madhukartemba/ir_hub/3D Print/Version 0/Led Ring.stl

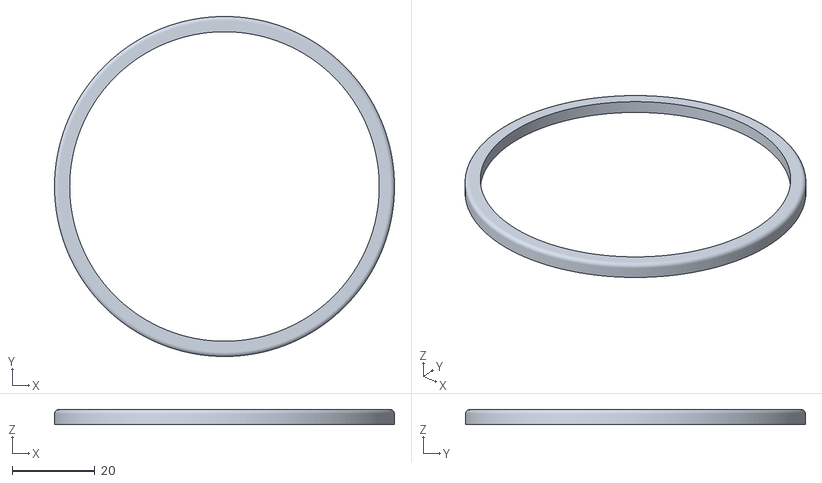
[picture p15: CAD file, 2025-08-03, an earlier design]
3D Print/Version 0/Led Ring.stl
82.4 x 82.4 x 3.60
