madhukartemba/ir_hub/3D Print/Version 1/Base5of5.stl

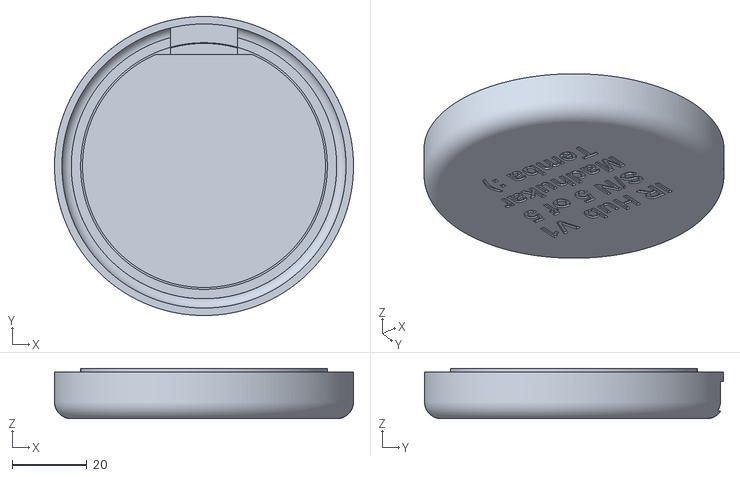
[picture p16: CAD file, 2025-08-30, an earlier design]
3D Print/Version 1/Base5of5.stl
80.0 x 80.0 x 13.5
