madhukartemba/ir_hub/3D Print/Version 0/Speaker Holder.stl

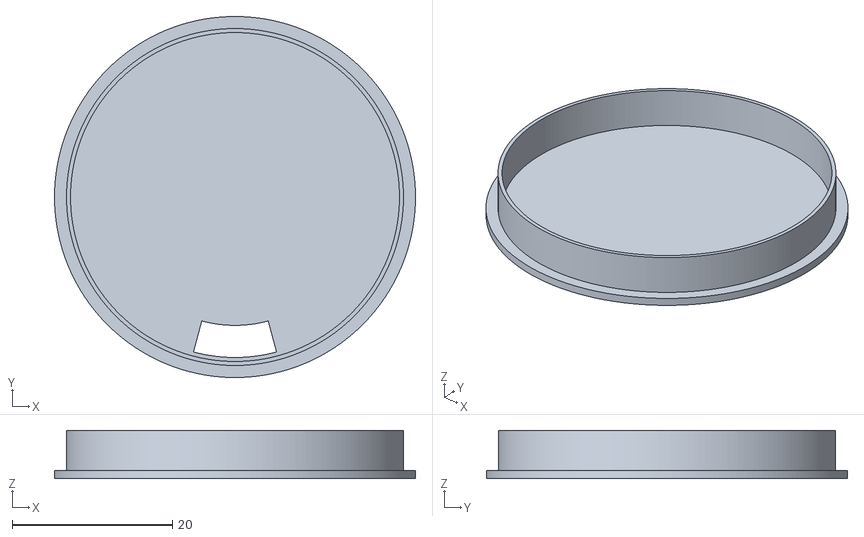
[picture p17: CAD file, 2025-08-03, an earlier design]
3D Print/Version 0/Speaker Holder.stl
45.0 x 45.0 x 6.00
