madhukartemba/ir_hub/src/UI/settings/Settings.h

#include <ESP.h>
#include "../../global/Global.h"
#include "../../preferences.h"
#include "../../utils/MenuUtils.h"
#include "ClearDataConfirmation.h"
#include "DisableAlexaConfirmation.h"
#include "FactoryResetConfirmation.h"
#include "MqttStatusDetailScreen.h"
#include "ResetWiFiConfirmation.h"
#include "SystemInfoScreen.h"
#include "UpdateCheckScreen.h"
#include "UserPrefs.h"

class Settings : public Screen {
   private:
    enum class MenuLevel {
        ROOT,
        PREFERENCES,
        CONNECTIVITY,
        UPDATES,
        SYSTEM,
        DATA_RESET,
    };

    enum class Action {
        OPEN_PREFERENCES,
        OPEN_CONNECTIVITY,
        OPEN_UPDATES,
        OPEN_SYSTEM,
        OPEN_DATA_RESET,
        SOUND,
        ALEXA,
        HAPTICS,
        FIRMWARE_INFO,
        LAST_CHECK_INFO,
        UPDATE_STATUS_INFO,
        MQTT_STATUS_INFO,
        INFO_SCREEN,
        CHECK_UPDATE,
        RESTART,
        CLEAR_DATA,
        WIFI_WIPE,
        FACTORY_RESET,
        BACK,
    };

    static constexpr int kMaxItems = 14;
    const char* menuItems[kMaxItems];
    Action menuActions[kMaxItems];
    int menuCount = 0;
    MenuLevel currentMenu = MenuLevel::ROOT;

    int selectedIndex = 0;
    bool isRestarting = false;
    unsigned long restartStartTime = 0;
    bool hasHaptics = false;
    bool hasOta = false;

    char firmwareLabel[28] = "Firmware: --";
    char lastCheckLabel[28] = "Last check: --";
    char updateStatusLabel[28] = "Status: Never checked";
    char mqttStatusLabel[24] = "MQTT: --";

   public:
    void onEnter() override {
        LOG_DEBUG("[Settings] onEnter");

        hasHaptics = haptics.isPresent();  // isPresent, not isReady (uncalibrated chip)
        hasOta = otaUpdater.isEnabled();
        currentMenu = MenuLevel::ROOT;
        buildMenuForCurrentLevel();
        selectedIndex = 0;
        isRestarting = false;

        ledRing.breathe(COLOR_SETTINGS);

        button.setClickCallback([this]() {
            LOG_DEBUG("[Settings] onButtonClick");
            if (isRestarting) {
                return;
            }
            selectedIndex = (selectedIndex + 1) % menuCount;
        });

        button.setLongPressCallback([this]() {
            LOG_DEBUG("[Settings] onButtonLongPress");
            if (isRestarting) {
                return;
            }
            handleAction(menuActions[selectedIndex]);
        });
    }

    void onUpdate() override {
        display.clear();

        if (isRestarting) {
            drawRestarting();
            if (millis() - restartStartTime > 2000) {
                ESP.restart();
            }
        } else {
            refreshDynamicLabels();
            drawMenu();
        }

        display.update();
    }

    void onExit() override { LOG_DEBUG("[Settings] onExit"); }

   private:
    void buildMenuForCurrentLevel() {
        menuCount = 0;

        switch (currentMenu) {
            case MenuLevel::ROOT:
                addRow(Action::OPEN_PREFERENCES);
                addRow(Action::OPEN_CONNECTIVITY);
                addRow(Action::OPEN_UPDATES);
                addRow(Action::OPEN_SYSTEM);
                addRow(Action::OPEN_DATA_RESET);
                addRow(Action::BACK);
                break;
            case MenuLevel::PREFERENCES:
                addRow(Action::SOUND);
                if (hasHaptics) {
                    addRow(Action::HAPTICS);
                }
                addRow(Action::BACK);
                break;
            case MenuLevel::CONNECTIVITY:
                addRow(Action::WIFI_WIPE);
                addRow(Action::ALEXA);
                addRow(Action::MQTT_STATUS_INFO);
                addRow(Action::BACK);
                break;
            case MenuLevel::UPDATES:
                if (hasOta) {
                    addRow(Action::CHECK_UPDATE);
                    addRow(Action::FIRMWARE_INFO);
                    addRow(Action::LAST_CHECK_INFO);
                    addRow(Action::UPDATE_STATUS_INFO);
                } else {
                    addRow(Action::UPDATE_STATUS_INFO);
                }
                addRow(Action::BACK);
                break;
            case MenuLevel::SYSTEM:
                addRow(Action::INFO_SCREEN);
                addRow(Action::RESTART);
                addRow(Action::BACK);
                break;
            case MenuLevel::DATA_RESET:
                addRow(Action::CLEAR_DATA);
                addRow(Action::FACTORY_RESET);
                addRow(Action::BACK);
                break;
        }
    }

    void addRow(Action action) {
        if (menuCount >= kMaxItems) {
            return;
        }
        menuActions[menuCount] = action;
        menuItems[menuCount] = labelFor(action);
        menuCount++;
    }

    void refreshDynamicLabels() {
        if (hasOta) {
            refreshOtaInfoLabels();
        }
        refreshMqttStatusLabel();
        for (int i = 0; i < menuCount; i++) {
            menuItems[i] = labelFor(menuActions[i]);
        }
    }

    void refreshOtaInfoLabels() {
        snprintf(firmwareLabel, sizeof(firmwareLabel), "Firmware: v%s",
                 otaUpdater.currentVersion());

        if (!otaUpdater.hasCompletedCheck()) {
            snprintf(lastCheckLabel, sizeof(lastCheckLabel), "Last check: --");
        } else {
            unsigned long ageMin = otaUpdater.lastCheckAgeMs() / 60000UL;
            if (ageMin < 60UL) {
                snprintf(lastCheckLabel, sizeof(lastCheckLabel), "Last check: %lum ago", ageMin);
            } else {
                unsigned long ageHours = ageMin / 60UL;
                snprintf(lastCheckLabel, sizeof(lastCheckLabel), "Last check: %luh ago", ageHours);
            }
        }

        snprintf(updateStatusLabel, sizeof(updateStatusLabel), "Status: %s",
                 otaUpdater.lastCheckStatusText());
    }

    void refreshMqttStatusLabel() {
        if (!wifiManager.isConnected()) {
            snprintf(mqttStatusLabel, sizeof(mqttStatusLabel), "MQTT: Offline");
            return;
        }
        if (!mqttConnector.isEnabled()) {
            snprintf(mqttStatusLabel, sizeof(mqttStatusLabel), "MQTT: Disabled");
            return;
        }
        if (mqttConnector.isConnected()) {
            snprintf(mqttStatusLabel, sizeof(mqttStatusLabel), "MQTT: Connected");
            return;
        }
        if (mqttConnector.hasError()) {
            snprintf(mqttStatusLabel, sizeof(mqttStatusLabel), "MQTT: Error");
            return;
        }
        snprintf(mqttStatusLabel, sizeof(mqttStatusLabel), "MQTT: Connecting");
    }

    const char* labelFor(Action action) {
        switch (action) {
            case Action::OPEN_PREFERENCES:
                return "Preferences";
            case Action::OPEN_CONNECTIVITY:
                return "Connectivity";
            case Action::OPEN_UPDATES:
                return "Updates";
            case Action::OPEN_SYSTEM:
                return "System";
            case Action::OPEN_DATA_RESET:
                return "Reset";
            case Action::SOUND:
                return userPrefsSoundEnabled() ? "Sound: On" : "Sound: Off";
            case Action::ALEXA:
                return userPrefsAlexaEnabled() ? "Alexa: On" : "Alexa: Off";
            case Action::HAPTICS:
                return userPrefsHapticsEnabled() ? "Haptics: On" : "Haptics: Off";
            case Action::FIRMWARE_INFO:
                return firmwareLabel;
            case Action::LAST_CHECK_INFO:
                return lastCheckLabel;
            case Action::UPDATE_STATUS_INFO:
                return updateStatusLabel;
            case Action::MQTT_STATUS_INFO:
                return mqttStatusLabel;
            case Action::INFO_SCREEN:
                return "Info";
            case Action::CHECK_UPDATE:
                return "Check for Updates";
            case Action::RESTART:
                return "Restart";
            case Action::CLEAR_DATA:
                return "Remove Devices";
            case Action::WIFI_WIPE:
                return "Configure Wi-Fi/MQTT";
            case Action::FACTORY_RESET:
                return "Factory Reset";
            case Action::BACK:
                return "Back";
        }
        return "?";
    }

    void handleAction(Action action) {
        switch (action) {
            case Action::OPEN_PREFERENCES:
                currentMenu = MenuLevel::PREFERENCES;
                selectedIndex = 0;
                buildMenuForCurrentLevel();
                break;
            case Action::OPEN_CONNECTIVITY:
                currentMenu = MenuLevel::CONNECTIVITY;
                selectedIndex = 0;
                buildMenuForCurrentLevel();
                break;
            case Action::OPEN_UPDATES:
                currentMenu = MenuLevel::UPDATES;
                selectedIndex = 0;
                buildMenuForCurrentLevel();
                break;
            case Action::OPEN_SYSTEM:
                currentMenu = MenuLevel::SYSTEM;
                selectedIndex = 0;
                buildMenuForCurrentLevel();
                break;
            case Action::OPEN_DATA_RESET:
                currentMenu = MenuLevel::DATA_RESET;
                selectedIndex = 0;
                buildMenuForCurrentLevel();
                break;
            case Action::SOUND:
                toggleSound();
                break;
            case Action::ALEXA:
                toggleAlexa();
                break;
            case Action::HAPTICS:
                toggleHaptics();
                break;
            case Action::FIRMWARE_INFO:
            case Action::LAST_CHECK_INFO:
            case Action::UPDATE_STATUS_INFO:
                // Read-only rows.
                speaker.shortBeep();
                break;
            case Action::MQTT_STATUS_INFO:
                speaker.shortBeep();
                router.push(new MqttStatusDetailScreen());
                break;
            case Action::INFO_SCREEN:
                LOG_DEBUG("[Settings] onButtonLongPress INFO_SCREEN");
                speaker.shortBeep();
                router.push(new SystemInfoScreen());
                break;
            case Action::CHECK_UPDATE:
                LOG_DEBUG("[Settings] onButtonLongPress CHECK_UPDATE");
                speaker.shortBeep();
                router.push(new UpdateCheckScreen());
                break;
            case Action::RESTART:
                LOG_DEBUG("[Settings] onButtonLongPress RESTART");
                isRestarting = true;
                restartStartTime = millis();
                break;
            case Action::CLEAR_DATA:
                LOG_DEBUG("[Settings] onButtonLongPress CLEAR_DATA");
                router.push(new ClearDataConfirmation());
                break;
            case Action::WIFI_WIPE:
                LOG_DEBUG("[Settings] onButtonLongPress WIFI_WIPE");
                router.push(new ResetWiFiConfirmation());
                break;
            case Action::FACTORY_RESET:
                LOG_DEBUG("[Settings] onButtonLongPress FACTORY_RESET");
                router.push(new FactoryResetConfirmation());
                break;
            case Action::BACK:
                if (currentMenu == MenuLevel::ROOT) {
                    LOG_DEBUG("[Settings] onButtonLongPress BACK (root)");
                    router.pop();
                } else {
                    LOG_DEBUG("[Settings] onButtonLongPress BACK (submenu)");
                    currentMenu = MenuLevel::ROOT;
                    selectedIndex = 0;
                    buildMenuForCurrentLevel();
                }
                break;
        }
    }

    void toggleSound() {
        bool newState = !userPrefsSoundEnabled();
        userPrefsSetSoundEnabled(newState);
        speaker.setMuted(!newState);
        if (newState) {
            speaker.shortBeep();  // confirmation only when turning ON
        }
        LOG_INFO("[Settings] Sound %s", newState ? "ON" : "OFF");
    }

    void toggleHaptics() {
        bool newState = !userPrefsHapticsEnabled();
        userPrefsSetHapticsEnabled(newState);

        if (newState) {
            // Lazy auto-calibration on first re-enable this boot. The LRA
            // buzzes briefly during cal — that's expected user feedback.
            if (!haptics.isReady() && haptics.isPresent()) {
                display.clear();
                display.setTextSize(1);
                display.printCentered("Calibrating", 24);
                display.printCentered("haptics...", 36);
                display.update();
                if (!haptics.begin()) {
                    LOG_WARN("[Settings] DRV2605 calibration failed");
                }
            }
            haptics.setMuted(false);
            if (haptics.isReady()) {
                haptics.playSelection();
            }
        } else {
            haptics.setMuted(true);
        }

        LOG_INFO("[Settings] Haptics %s", newState ? "ON" : "OFF");
    }

    void toggleAlexa() {
        bool currentlyEnabled = userPrefsAlexaEnabled();
        if (currentlyEnabled) {
            // Disabling needs explicit confirmation.
            router.push(new DisableAlexaConfirmation());
            return;
        }

        userPrefsSetAlexaEnabled(true);
        speaker.shortBeep();

        if (wifiManager.isConnected()) {
            alexaConnector.begin();
        }
        LOG_INFO("[Settings] Alexa ON");
    }

    void drawMenu() {
        display.setTextSize(1);
        display.printCentered(titleForCurrentMenu(), 0);
        display.drawLine(0, 12, display.getWidth(), 12);
        MenuUtils::drawScrollableMenu(menuItems, menuCount, selectedIndex, 3, 20);
    }

    const char* titleForCurrentMenu() {
        switch (currentMenu) {
            case MenuLevel::ROOT:
                return "Settings";
            case MenuLevel::PREFERENCES:
                return "Preferences";
            case MenuLevel::CONNECTIVITY:
                return "Connectivity";
            case MenuLevel::SYSTEM:
                return "System";
            case MenuLevel::UPDATES:
                return "Updates";
            case MenuLevel::DATA_RESET:
                return "Reset";
        }
        return "Settings";
    }

    void drawRestarting() {
        display.clear();
        display.setTextSize(1);
        display.printCentered("Restarting...", 20);
        display.setTextSize(1);
        display.printCentered("Please wait", 35);
    }
};
