madhukartemba/ir_hub/src/UI/devices/DeviceActions.h

#include <Arduino.h>
#include "../../config.h"
#include "../../global/Global.h"
#include "../../led/ClickSweepOnceAnimation.h"
#include "../../preferences.h"
#include "../../utils/MenuUtils.h"
#include "DeviceDeleteConfirmation.h"
#include "DeviceDetails.h"

class DeviceActions : public Screen {
   private:
    enum class ActionType { ON, OFF, DETAILS, REMOVE, BACK };

    Device device;
    ActionType selectedAction;
    int selectedIndex;
    const char* actions[5] = {"Send ON", "Send OFF", "Details", "Delete Device", "Back"};

   public:
    explicit DeviceActions(const Device& device)
        : device(device), selectedAction(ActionType::ON), selectedIndex(0) {}

    void onEnter() override {
        LOG_DEBUG("[DeviceActions] onEnter for device %s", device.uuid.c_str());
        ledRing.breathe(COLOR_INFO_DARK);

        button.setClickCallback([this]() {
            LOG_DEBUG("[DeviceActions] onButtonClick");
            // Navigate through actions
            selectedIndex = (selectedIndex + 1) % 5;
            selectedAction = static_cast<ActionType>(selectedIndex);
        });

        button.setLongPressCallback([this]() {
            LOG_DEBUG("[DeviceActions] onButtonLongPress");
            switch (selectedAction) {
                case ActionType::ON:
                case ActionType::OFF:
                    // Execute ON or OFF action
                    executeAction();
                    break;
                case ActionType::DETAILS:
                    // Navigate to details
                    router.push(new DeviceDetails(device));
                    break;
                case ActionType::REMOVE:
                    // Navigate to delete confirmation
                    router.push(new DeviceDeleteConfirmation(device));
                    break;
                case ActionType::BACK:
                    // Go back to devices list
                    router.pop();
                    break;
            }
        });
    }

    void onUpdate() override {
        display.clear();
        displayActions();
        display.update();
    }

    void displayActions() {
        // Show title with short device id (first 6 chars of the 32-char uuid).
        // Full uuid is too wide for a 128px OLED.
        display.setTextSize(1);
        String title = "Device " + device.uuid.substring(0, 6);
        display.printCentered(title.c_str(), 0);

        display.drawLine(0, 12, display.getWidth(), 12);

        // Use the scrollable menu utility
        MenuUtils::drawScrollableMenu(actions, 5, selectedIndex, 3, 20);
    }

    void executeAction() {
        switch (selectedAction) {
            case ActionType::ON:
                if (device.onCommand.isValid()) {
                    LOG_INFO("[DeviceActions] Sending ON command for device %s",
                             device.uuid.c_str());
                    irManager.sendProtocol(device.onCommand);
                    ledRing.addAnimation(
                        std::make_unique<ClickSweepOnceAnimation>(NUM_LEDS, SEND_ON_COMMAND_COLOR));
                } else {
                    LOG_ERROR("[DeviceActions] Invalid ON command for device %s",
                              device.uuid.c_str());
                    display.clear();
                    display.printCentered("Invalid ON command", 30);
                    display.update();
                    delay(2000);
                }
                break;

            case ActionType::OFF:
                if (device.offCommand.isValid()) {
                    LOG_INFO("[DeviceActions] Sending OFF command for device %s",
                             device.uuid.c_str());
                    irManager.sendProtocol(device.offCommand);
                    ledRing.addAnimation(std::make_unique<ClickSweepOnceAnimation>(
                        NUM_LEDS, SEND_OFF_COMMAND_COLOR));
                } else {
                    LOG_ERROR("[DeviceActions] Invalid OFF command for device %s",
                              device.uuid.c_str());
                    display.clear();
                    display.printCentered("Invalid OFF command", 30);
                    display.update();
                    delay(2000);
                }
                break;
            default:
                LOG_ERROR("[DeviceActions] Unhandled action type in executeAction: %d",
                          static_cast<int>(selectedAction));
        }
    }

    void onExit() override { LOG_DEBUG("[DeviceActions] onExit"); }
};
