madhukartemba/ir_hub/src/UI/settings/FactoryResetConfirmation.h

#include <ESP8266WiFi.h>
#include <LittleFS.h>
#include "PendingOta.h"
#include "../../global/Global.h"
#include "../../preferences.h"

class FactoryResetConfirmation : public Screen {
   public:
    void onEnter() override {
        LOG_DEBUG("[FactoryResetConfirmation] onEnter");
        ledRing.breathe(COLOR_ERROR);

        button.setClickCallback([this]() {
            LOG_DEBUG("[FactoryResetConfirmation] onButtonClick - Exit");
            router.pop();
        });

        button.setLongPressCallback([this]() {
            LOG_DEBUG("[FactoryResetConfirmation] onButtonLongPress - Confirm");
            factoryResetAndRestart();
        });
    }

    void onUpdate() override {
        display.drawConfirmLongPress("Factory Reset?", "Will reset Wi-Fi", "+ all saved data",
                                     "+ pending OTA");
        display.update();
    }

    void onExit() override {
        LOG_DEBUG("[FactoryResetConfirmation] onExit");
    }

   private:
    void factoryResetAndRestart() {
        display.clear();
        display.setTextSize(1);
        display.drawConfirmBody2("Factory reset...", "Please wait");
        display.update();
        ledRing.solid(COLOR_ERROR);
        ledRing.finishTransition();

        LOG_INFO("[FactoryReset] Shutting down MQTT + Wi-Fi");
        mqttConnector.shutdown();
        WiFi.disconnect(true);
        delay(150);

        LOG_INFO("[FactoryReset] Clearing Wi-Fi credentials");
        wifiManager.resetWiFi();

        LOG_INFO("[FactoryReset] Clearing pending OTA RTC slot");
        pending_ota::clear();

        LOG_INFO("[FactoryReset] Formatting LittleFS");
        bool fsOk = LittleFS.format();
        LOG_INFO("[FactoryReset] LittleFS.format() returned %s", fsOk ? "true" : "false");

        if (fsOk) {
            speaker.successBeep();
            display.clear();
            display.setTextSize(1);
            display.drawConfirmBody2("Factory reset done", "Restarting...");
        } else {
            speaker.errorBeep();
            display.clear();
            display.setTextSize(1);
            display.drawConfirmBody2("Reset partial", "Restarting...");
        }
        display.update();
        delay(900);
        ESP.restart();
    }
};
